Team-Xbots/PID-Line-Following-Robot/hardware/Component_&_Connection/LM2596 DC-DC Step Down.webp

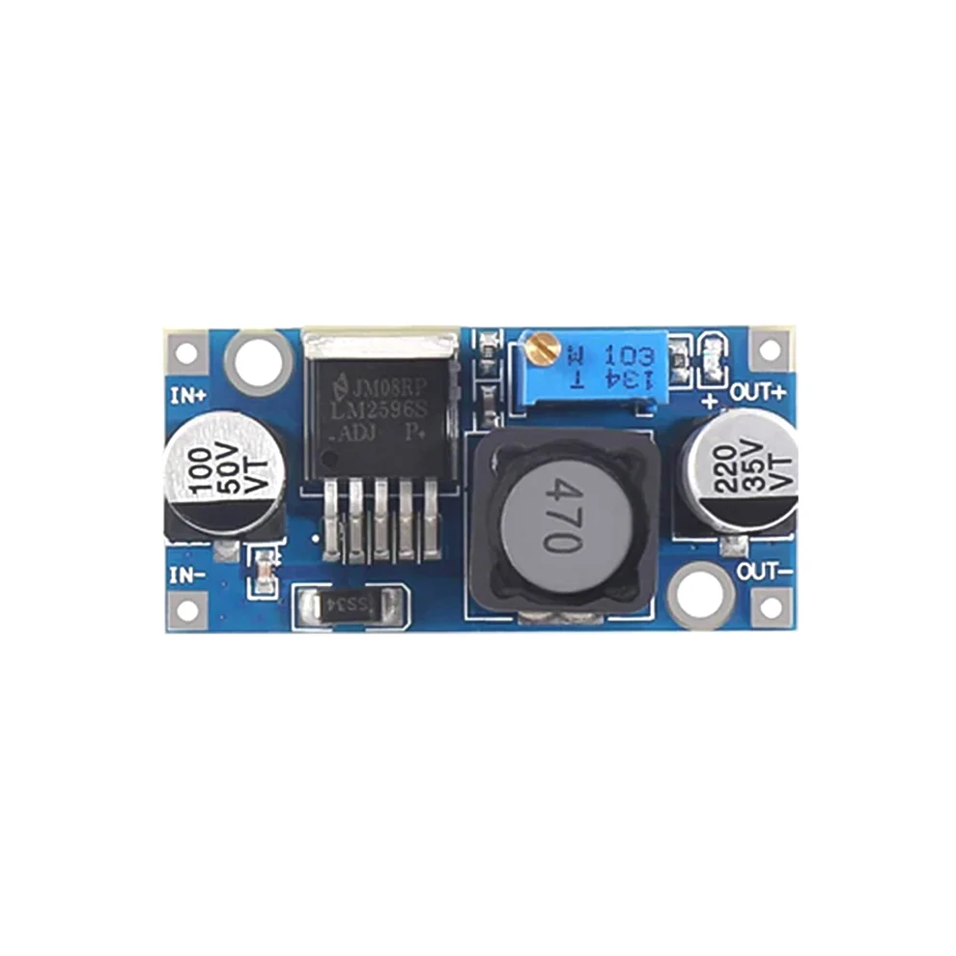
hardware/Component_&_Connection/LM2596 DC-DC Step Down.webp
