Team-Xbots/PID-Line-Following-Robot/hardware/Component_&_Connection/AMS1117.png

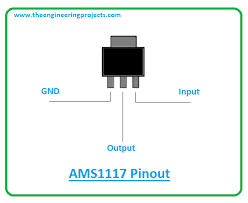
hardware/Component_&_Connection/AMS1117.png
