Team-Xbots/PID-Line-Following-Robot/hardware/Component_&_Connection/esp32_38pins.png

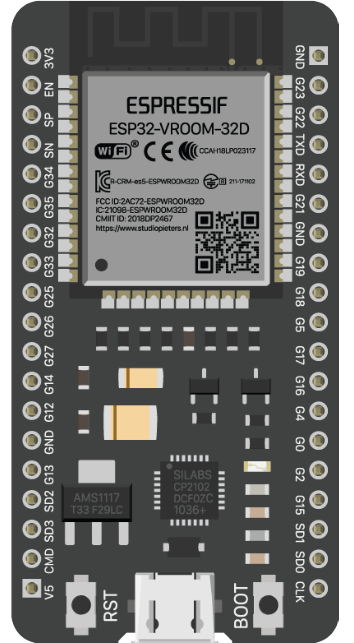
hardware/Component_&_Connection/esp32_38pins.png
