Team-Xbots/PID-Line-Following-Robot/hardware/Component_&_Connection/Small Ball Caster.png

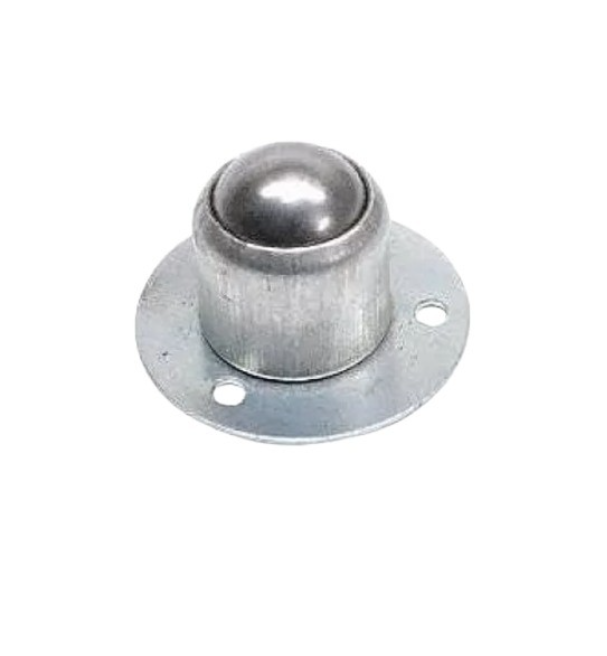
hardware/Component_&_Connection/Small Ball Caster.png
