Team-Xbots/PID-Line-Following-Robot/hardware/Component_&_Connection/tactile button.jpg

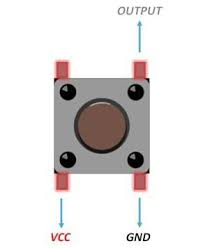
hardware/Component_&_Connection/tactile button.jpg
